Xinyuan-LilyGO/T-Wristband/firmware/T-Wristband-20191206/setting.jpg

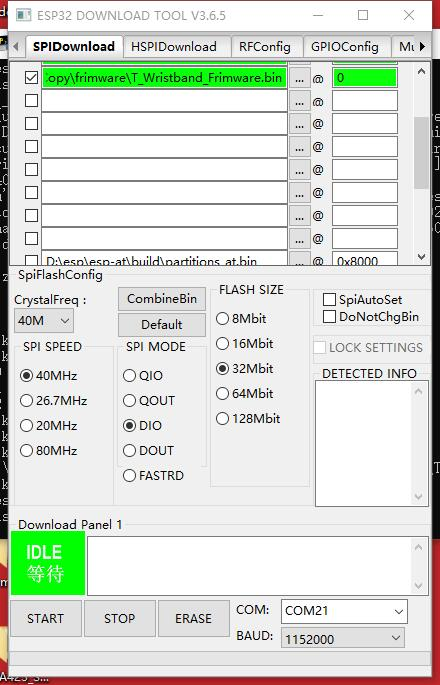
firmware/T-Wristband-20191206/setting.jpg
