Xinyuan-LilyGO/T-Wristband/libdeps/SparkFun_MAX3010x_Sensor_Library/src/heartRate.cpp

/*
 Optical Heart Rate Detection (PBA Algorithm)
 By: Nathan Seidle
 SparkFun Electronics
 Date: October 2nd, 2016
 
 Given a series of IR samples from the MAX30105 we discern when a heart beat is occurring

 Let's have a brief chat about what this code does. We're going to try to detect
 heart-rate optically. This is tricky and prone to give false readings. We really don't
 want to get anyone hurt so use this code only as an example of how to process optical
 data. Build fun stuff with our MAX30105 breakout board but don't use it for actual
 medical diagnosis.

 Excellent background on optical heart rate detection:
 http://www.ti.com/lit/an/slaa655/slaa655.pdf

 Good reading:
 http://www.techforfuture.nl/fjc_documents/mitrabaratchi-measuringheartratewithopticalsensor.pdf
 https://fruct.org/publications/fruct13/files/Lau.pdf

 This is an implementation of Maxim's PBA (Penpheral Beat Amplitude) algorithm. It's been 
 converted to work within the Arduino framework.
*/

/* Copyright (C) 2016 Maxim Integrated Products, Inc., All Rights Reserved.
*
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
* Except as contained in this notice, the name of Maxim Integrated
* Products, Inc. shall not be used except as stated in the Maxim Integrated
* Products, Inc. Branding Policy.
*
* The mere transfer of this software does not imply any licenses
* of trade secrets, proprietary technology, copyrights, patents,
* trademarks, maskwork rights, or any other form of intellectual
* property whatsoever. Maxim Integrated Products, Inc. retains all
* ownership rights.
* 
*/

#include "heartRate.h"

int16_t IR_AC_Max = 20;
int16_t IR_AC_Min = -20;

int16_t IR_AC_Signal_Current = 0;
int16_t IR_AC_Signal_Previous;
int16_t IR_AC_Signal_min = 0;
int16_t IR_AC_Signal_max = 0;
int16_t IR_Average_Estimated;

int16_t positiveEdge = 0;
int16_t negativeEdge = 0;
int32_t ir_avg_reg = 0;

int16_t cbuf[32];
uint8_t offset = 0;

static const uint16_t FIRCoeffs[12] = {172, 321, 579, 927, 1360, 1858, 2390, 2916, 3391, 3768, 4012, 4096};

//  Heart Rate Monitor functions takes a sample value and the sample number
//  Returns true if a beat is detected
//  A running average of four samples is recommended for display on the screen.
bool checkForBeat(int32_t sample)
{
  bool beatDetected = false;

  //  Save current state
  IR_AC_Signal_Previous = IR_AC_Signal_Current;
  
  //This is good to view for debugging
  //Serial.print("Signal_Current: ");
  //Serial.println(IR_AC_Signal_Current);

  //  Process next data sample
  IR_Average_Estimated = averageDCEstimator(&ir_avg_reg, sample);
  IR_AC_Signal_Current = lowPassFIRFilter(sample - IR_Average_Estimated);

  //  Detect positive zero crossing (rising edge)
  if ((IR_AC_Signal_Previous < 0) & (IR_AC_Signal_Current >= 0))
  {
  
    IR_AC_Max = IR_AC_Signal_max; //Adjust our AC max and min
    IR_AC_Min = IR_AC_Signal_min;

    positiveEdge = 1;
    negativeEdge = 0;
    IR_AC_Signal_max = 0;

    //if ((IR_AC_Max - IR_AC_Min) > 100 & (IR_AC_Max - IR_AC_Min) < 1000)
    if ((IR_AC_Max - IR_AC_Min) > 20 & (IR_AC_Max - IR_AC_Min) < 1000)
    {
      //Heart beat!!!
      beatDetected = true;
    }
  }

  //  Detect negative zero crossing (falling edge)
  if ((IR_AC_Signal_Previous > 0) & (IR_AC_Signal_Current <= 0))
  {
    positiveEdge = 0;
    negativeEdge = 1;
    IR_AC_Signal_min = 0;
  }

  //  Find Maximum value in positive cycle
  if (positiveEdge & (IR_AC_Signal_Current > IR_AC_Signal_Previous))
  {
    IR_AC_Signal_max = IR_AC_Signal_Current;
  }

  //  Find Minimum value in negative cycle
  if (negativeEdge & (IR_AC_Signal_Current < IR_AC_Signal_Previous))
  {
    IR_AC_Signal_min = IR_AC_Signal_Current;
  }
  
  return(beatDetected);
}

//  Average DC Estimator
int16_t averageDCEstimator(int32_t *p, uint16_t x)
{
  *p += ((((long) x << 15) - *p) >> 4);
  return (*p >> 15);
}

//  Low Pass FIR Filter
int16_t lowPassFIRFilter(int16_t din)
{  
  cbuf[offset] = din;

  int32_t z = mul16(FIRCoeffs[11], cbuf[(offset - 11) & 0x1F]);
  
  for (uint8_t i = 0 ; i < 11 ; i++)
  {
    z += mul16(FIRCoeffs[i], cbuf[(offset - i) & 0x1F] + cbuf[(offset - 22 + i) & 0x1F]);
  }

  offset++;
  offset %= 32; //Wrap condition

  return(z >> 15);
}

//  Integer multiplier
int32_t mul16(int16_t x, int16_t y)
{
  return((long)x * (long)y);
}
