Xinyuan-LilyGO/T-Wristband/libdeps/Adafruit_DRV2605_Library/examples/basic/basic.ino

#include <Wire.h>
#include "Adafruit_DRV2605.h"

Adafruit_DRV2605 drv;

void setup() {
  Serial.begin(9600);
  Serial.println("DRV test");
  drv.begin();
  
  drv.selectLibrary(1);
  
  // I2C trigger by sending 'go' command 
  // default, internal trigger when sending GO command
  drv.setMode(DRV2605_MODE_INTTRIG); 
}

uint8_t effect = 1;

void loop() {
//  Serial.print("Effect #"); Serial.println(effect);

   if (effect == 1) {
    Serial.println("11.2 Waveform Library Effects List");
  }

  if (effect == 1) {
    Serial.println(F("1 − Strong Click - 100%"));
  }
  if (effect == 2) {
    Serial.println(F("2 − Strong Click - 60%"));
  }
  if (effect == 3) {
    Serial.println(F("3 − Strong Click - 30%"));
  }
  if (effect == 4) {
    Serial.println(F("4 − Sharp Click - 100%"));
  }
  if (effect == 5) {
    Serial.println(F("5 − Sharp Click - 60%"));
  }
  if (effect == 6) {
    Serial.println(F("6 − Sharp Click - 30%"));
  }
  if (effect == 7) {
    Serial.println(F("7 − Soft Bump - 100%"));
  }
  if (effect == 8) {
    Serial.println(F("8 − Soft Bump - 60%"));
  }
  if (effect == 9) {
    Serial.println(F("9 − Soft Bump - 30%"));
  }
  if (effect == 10) {
    Serial.println(F("10 − Double Click - 100%"));
  }
  if (effect == 11) {
    Serial.println(F("11 − Double Click - 60%"));
  }
  if (effect == 12) {
    Serial.println(F("12 − Triple Click - 100%"));
  }
  if (effect == 13) {
    Serial.println(F("13 − Soft Fuzz - 60%"));
  }
  if (effect == 14) {
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
    Serial.println(F("121 − Smooth Hum 3 (No kick or brake pulse) – 30%"));
  }
  if (effect == 122) {
    Serial.println(F("122 − Smooth Hum 4 (No kick or brake pulse) – 20%"));
  }
  if (effect == 123) {
    Serial.println(F("123 − Smooth Hum 5 (No kick or brake pulse) – 10%"));
  }

  // set the effect to play
  drv.setWaveform(0, effect);  // play effect 
  drv.setWaveform(1, 0);       // end waveform

  // play the effect!
  drv.go();

  // wait a bit
  delay(500);

  effect++;
  if (effect > 117) effect = 1;
}
