Xinyuan-LilyGO/T-Wristband/libdeps/Adafruit_DRV2605_Library/examples/realtime/realtime.ino

#include <Wire.h>
#include "Adafruit_DRV2605.h"

Adafruit_DRV2605 drv;

void setup() {
  Serial.begin(9600);
  Serial.println("DRV test");
  drv.begin();
    
  // Set Real-Time Playback mode
  drv.setMode(DRV2605_MODE_REALTIME);
}

uint8_t rtp_index = 0;
uint8_t rtp[] = {
  0x30, 100, 0x32, 100, 
  0x34, 100, 0x36, 100, 
  0x38, 100, 0x3A, 100,
  0x00, 100,
  0x40, 200, 0x00, 100, 
  0x40, 200, 0x00, 100, 
  0x40, 200, 0x00, 100
};

void loop() {

  if (rtp_index < sizeof(rtp)/sizeof(rtp[0])) {
    drv.setRealtimeValue(rtp[rtp_index]);
    rtp_index++;
    delay(rtp[rtp_index]);
    rtp_index++;
  } else {
    drv.setRealtimeValue(0x00);
    delay(1000);
    rtp_index = 0;
  }
  
}
