Xinyuan-LilyGO/T-Wristband/examples/T-Wristband-DRV2605/charge.h

// Dimensions    : 16x16 pixels
// Size          : 512 Bytes
const unsigned short  charge[0x100] ={
0x0000, 0x0000, 0x0000, 0x0000, 0x0000, 0x0000, 0x0000, 0x0000, 0x0000, 0x0000, 0x0000, 0x0000, 0x0000, 0x0000, 0x0000, 0x0000,   // 0x0010 (16)
0x0000, 0x0000, 0x0000, 0x0000, 0x0000, 0x0000, 0xD10E, 0xD10E, 0xD10E, 0xD10E, 0xD10E, 0xD10E, 0xD10E, 0x0000, 0x0000, 0x0000,   // 0x0020 (32)
0x0000, 0x0000, 0x0000, 0x0000, 0x0000, 0x0000, 0xD10F, 0xD10F, 0xD10F, 0xD10F, 0xD10F, 0xD10F, 0x0000, 0x0000, 0x0000, 0x0000,   // 0x0030 (48)
0x0000, 0x0000, 0x0000, 0x0000, 0x0000, 0xD10F, 0xD10F, 0xD10F, 0xD10F, 0xD10F, 0xD10F, 0xD10F, 0x0000, 0x0000, 0x0000, 0x0000,   // 0x0040 (64)
0x0000, 0x0000, 0x0000, 0x0000, 0x0000, 0xD10F, 0xD10F, 0xD10F, 0xD10F, 0xD10F, 0xD10F, 0x0000, 0x0000, 0x0000, 0x0000, 0x0000,   // 0x0050 (80)
0x0000, 0x0000, 0x0000, 0x0000, 0xD10E, 0xD10F, 0xD10F, 0xD10F, 0xD10F, 0xD10F, 0xD10E, 0x0000, 0x0000, 0x0000, 0x0000, 0x0000,   // 0x0060 (96)
0x0000, 0x0000, 0x0000, 0x0000, 0xD10F, 0xD10F, 0xD10F, 0xD10F, 0xD10F, 0xD12F, 0x0000, 0x0000, 0x0000, 0x0000, 0x0000, 0x0000,   // 0x0070 (112)
0x0000, 0x0000, 0x0000, 0x0000, 0xD10F, 0xD10F, 0xD10F, 0xD10F, 0xD10F, 0xD10F, 0xD10F, 0xD12F, 0x0000, 0x0000, 0x0000, 0x0000,   // 0x0080 (128)
0x0000, 0x0000, 0x0000, 0xD10E, 0xD10E, 0xD10E, 0xD10F, 0xD10F, 0xD10F, 0xD10F, 0xD10F, 0x0000, 0x0000, 0x0000, 0x0000, 0x0000,   // 0x0090 (144)
0x0000, 0x0000, 0x0000, 0x0000, 0x0000, 0xD10F, 0xD10F, 0xD10F, 0xD10F, 0xD10E, 0x0000, 0x0000, 0x0000, 0x0000, 0x0000, 0x0000,   // 0x00A0 (160)
0x0000, 0x0000, 0x0000, 0x0000, 0x0000, 0xD10F, 0xD10F, 0xD10F, 0xD10F, 0x0000, 0x0000, 0x0000, 0x0000, 0x0000, 0x0000, 0x0000,   // 0x00B0 (176)
0x0000, 0x0000, 0x0000, 0x0000, 0x0000, 0xD10F, 0xD10F, 0xD10F, 0x0000, 0x0000, 0x0000, 0x0000, 0x0000, 0x0000, 0x0000, 0x0000,   // 0x00C0 (192)
0x0000, 0x0000, 0x0000, 0x0000, 0xD8EF, 0xD10F, 0xD10F, 0x0000, 0x0000, 0x0000, 0x0000, 0x0000, 0x0000, 0x0000, 0x0000, 0x0000,   // 0x00D0 (208)
0x0000, 0x0000, 0x0000, 0x0000, 0xD10F, 0xD10F, 0x0000, 0x0000, 0x0000, 0x0000, 0x0000, 0x0000, 0x0000, 0x0000, 0x0000, 0x0000,   // 0x00E0 (224)
0x0000, 0x0000, 0x0000, 0x0000, 0xD10F, 0x0000, 0x0000, 0x0000, 0x0000, 0x0000, 0x0000, 0x0000, 0x0000, 0x0000, 0x0000, 0x0000,   // 0x00F0 (240)
0x0000, 0x0000, 0x0000, 0x0000, 0x0000, 0x0000, 0x0000, 0x0000, 0x0000, 0x0000, 0x0000, 0x0000, 0x0000, 0x0000, 0x0000, 0x0000,   // 0x0100 (256)
};
